supreme-gg-gg/NeuroSteady/model/results/tsne.png

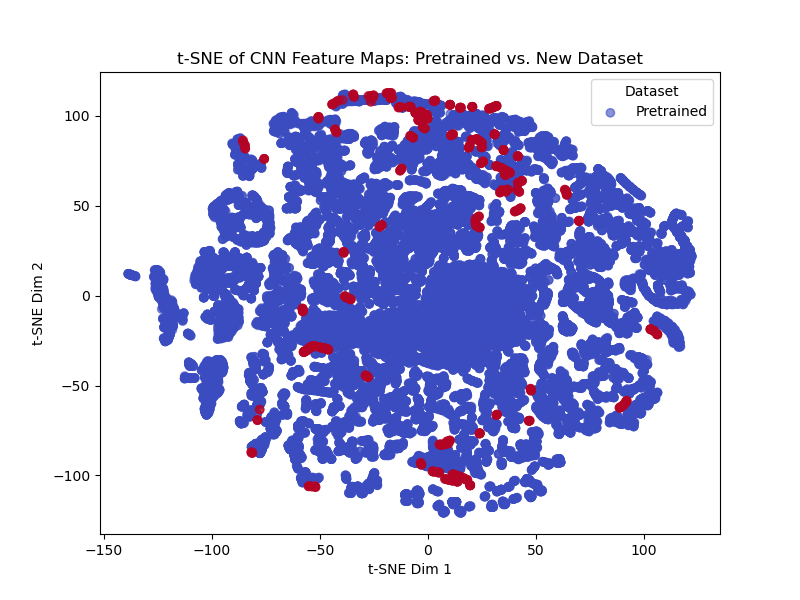
model/results/tsne.png
